vklachkov/blackgpib/history/usernameak+BOOtak/dumps/2023_06_17/Session 0_validate.txt

ATN change while low DAV at 3.557926500s!
DIO[6] change while low DAV at 3.561440563s!
DIO[4] change while low DAV at 3.565553000s!
ATN change while low DAV at 7.139637375s!
ATN change while low DAV at 7.158208313s!
DIO[4] change while low DAV at 7.161558750s!
DIO[1] change while low DAV at 7.161582688s!
ATN change while low DAV at 28.868063500s!
28.870067125: dt = 63 < 100 at Channel 0!
28.870069125: dt = 62 < 100 at Channel 2!
34.531450375: dt = 63 < 100 at Channel 2!
EOI change while low DAV at 39.049282750s!
39.051622688: dt = 63 < 100 at Channel 0!
39.051625562: dt = 62 < 100 at Channel 2!
44.164226687: dt = 62 < 100 at Channel 2, Channel 6!
45.249965438: dt = 63 < 100 at Channel 2!
EOI change while low DAV at 48.592852687s!
48.595399063: dt = 63 < 100 at Channel 2!
58.045957562: dt = 62 < 100 at Channel 2!
ATN change while low DAV at 58.778009062s!
ATN change while low DAV at 64.433681125s!
69.548303562: dt = 62 < 100 at Channel 2!
73.332542562: dt = 62 < 100 at Channel 2!
ATN change while low DAV at 75.814665125s!
ATN change while low DAV at 87.744416625s!
87.746567813: dt = 63 < 100 at Channel 2!
ATN change while low DAV at 99.673824875s!
99.676485750: dt = 62 < 100 at Channel 0!
99.676488187: dt = 62 < 100 at Channel 2!
109.121345437: dt = 62 < 100 at Channel 2!
111.500724812: dt = 62 < 100 at Channel 7!
111.500741125: dt = 63 < 100 at Channel 7!
111.500757437: dt = 62 < 100 at Channel 5, Channel 7!
111.500757500: dt = 63 < 100 at Channel 5, Channel 7!
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
111.503446563: dt = 63 < 100 at Channel 3!
111.503446938: dt = 63 < 100 at Channel 3!
111.503447125: dt = 62 < 100 at Channel 3!
111.503447562: dt = 62 < 100 at Channel 3!
111.503448000: dt = 63 < 100 at Channel 3!
111.503448625: dt = 63 < 100 at Channel 3!
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
